jruben4/Skynet-AirMultiSensor/Images/IMG_0809.jpeg

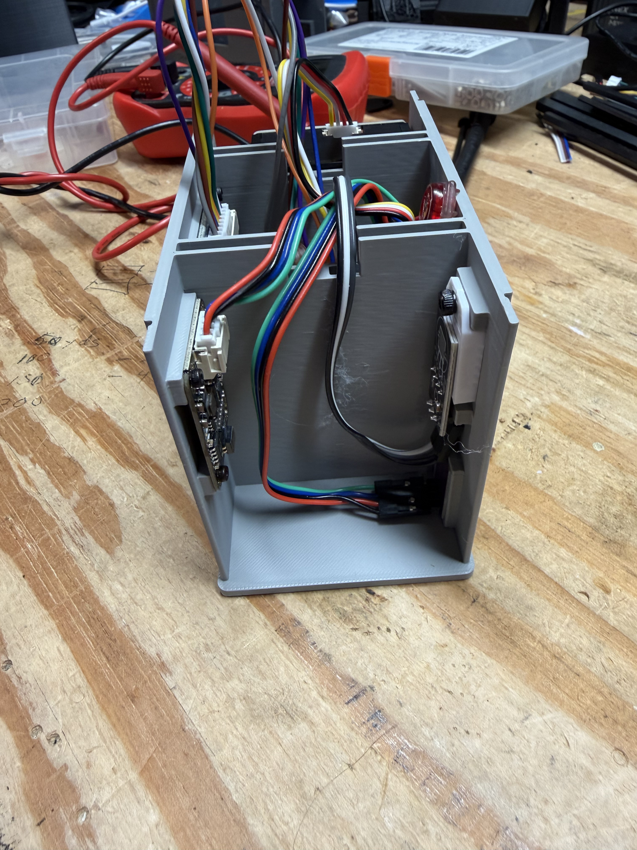
Images/IMG_0809.jpeg
