jruben4/Skynet-AirMultiSensor/Images/IMG_0810.jpeg

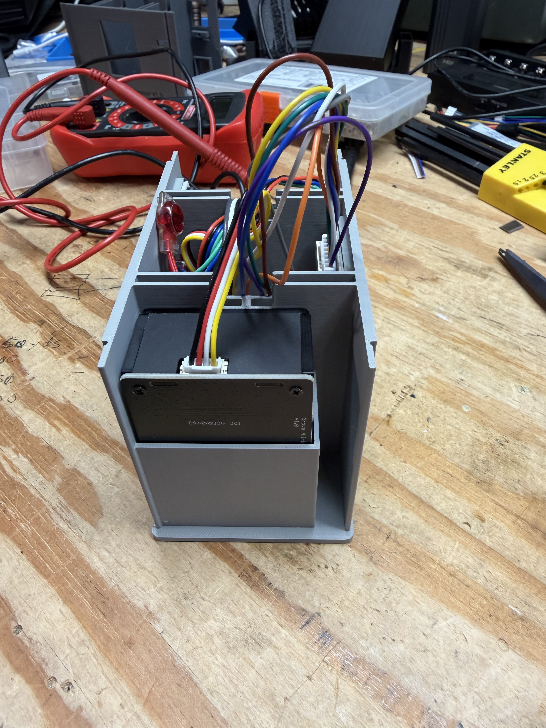
Images/IMG_0810.jpeg
