jruben4/Skynet-AirMultiSensor/Images/IMG_0812.JPG

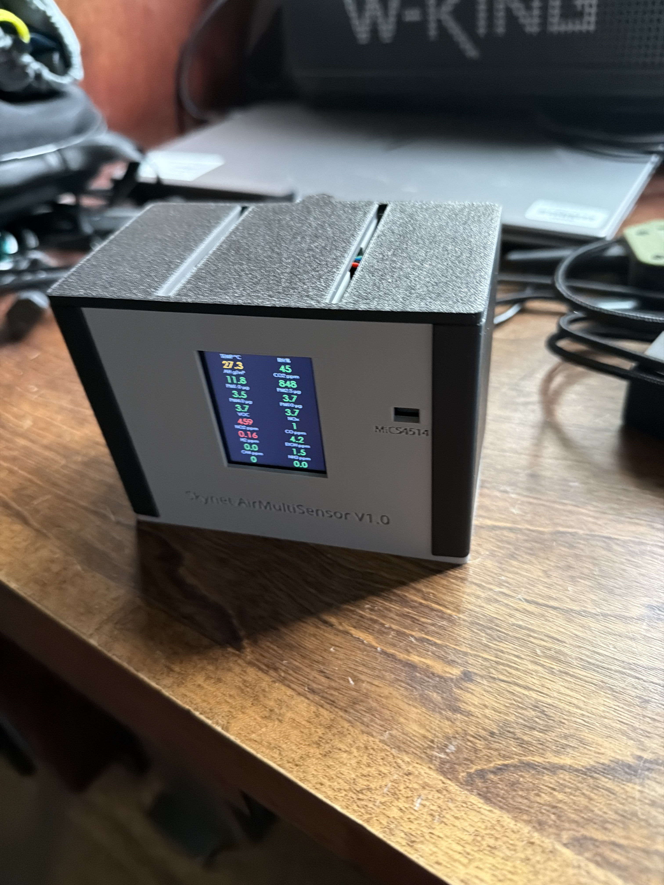
Images/IMG_0812.JPG
