jruben4/Skynet-AirMultiSensor/Images/IMG_0815.jpeg

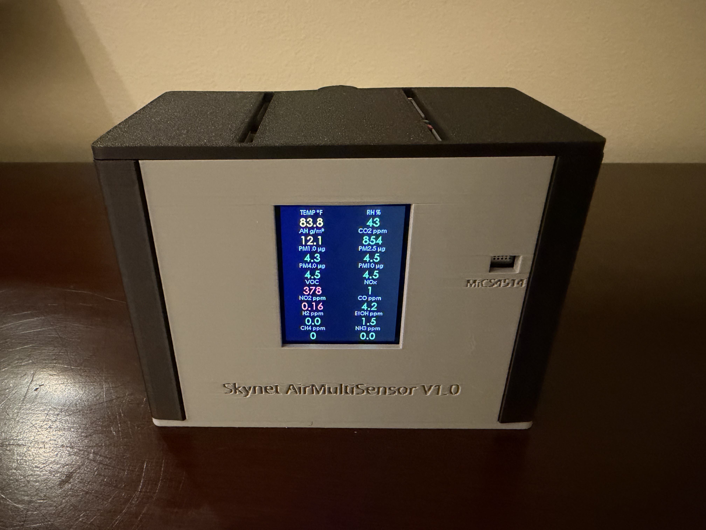
Images/IMG_0815.jpeg
