jruben4/Skynet-AirMultiSensor/Images/IMG_0813.JPG

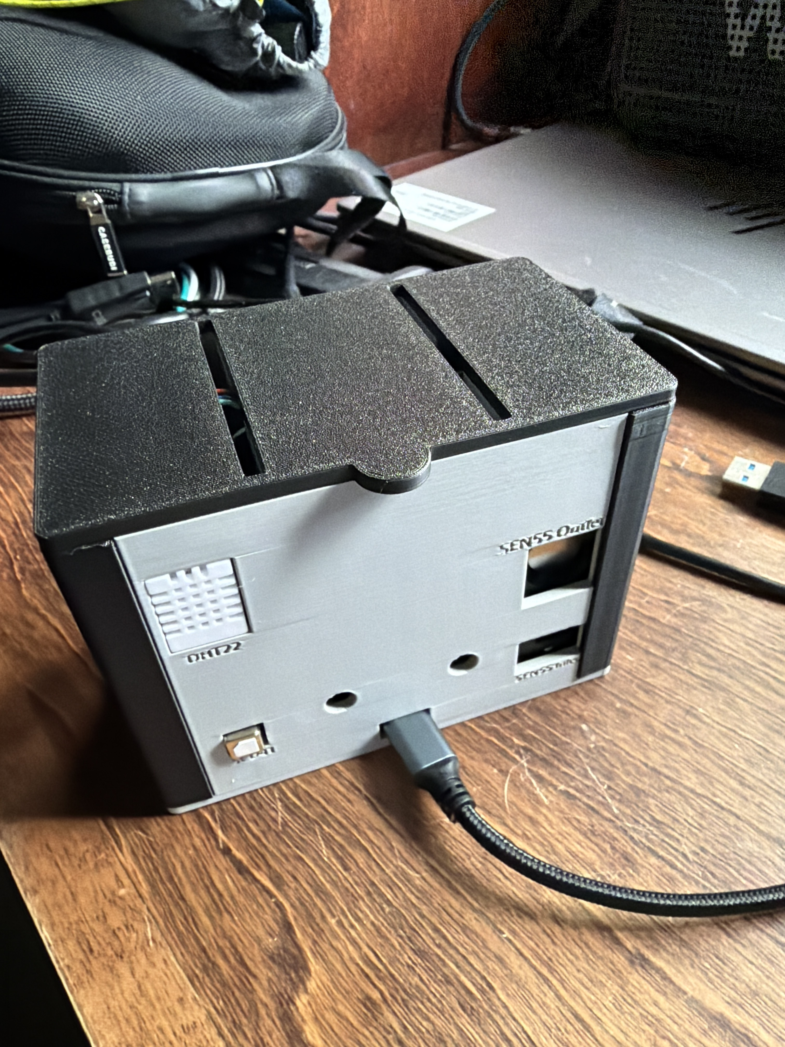
Images/IMG_0813.JPG
